gabebuckmaster/nixie_clock/firmware/Generic_F042Cx/variant.cpp

/*
 *******************************************************************************
 * Copyright (c) 2019, STMicroelectronics
 * All rights reserved.
 *
 * This software component is licensed by ST under BSD 3-Clause license,
 * the "License"; You may not use this file except in compliance with the
 * License. You may obtain a copy of the License at:
 *                        opensource.org/licenses/BSD-3-Clause
 *
 *******************************************************************************
 */

#include "pins_arduino.h"

#ifdef __cplusplus
extern "C" {
#endif

// Digital PinName array
// This array allows to wrap Arduino pin number(Dx or x)
// to STM32 PinName (PX_n)
// Arbitrarily chosen to be same as bluepill
const PinName digitalPin[] = {
  PB_9,  //D0
  PB_8,  //D1
  PB_7,  //D2
  PB_6,  //D3
  PB_5,  //D4
  PB_4,  //D5
  PB_3,  //D6
  PA_15, //D7
  PA_12, //D8 - USB DP
  PA_11, //D9 - USB DM
  PA_10, //D10
  PA_9,  //D11
  PA_8,  //D12
  PB_15, //D13
  PB_14, //D14
  PB_13, //D15
  PB_12, //D16
  /* Right side */
  PC_13, //D17
  PC_14, //D18
  PC_15, //D19
  PA_0,  //D20/A0
  PA_1,  //D21/A1
  PA_2,  //D22/A2
  PA_3,  //D23/A3
  PA_4,  //D24/A4
  PA_5,  //D25/A5
  PA_6,  //D26/A6
  PA_7,  //D27/A7
  PB_0,  //D28/A8
  PB_1,  //D29/A9
  PB_10, //D30
  PB_11, //D31
  PB_2,  //D32
  PA_13, //D33 - SWDI0
  PA_14, //D34 - SWCLK
};

// If analog pins are not contiguous in the digitalPin array:
// Add the analogInputPin array without defining NUM_ANALOG_FIRST
// Analog (Ax) pin number array
// where x is the index to retrieve the digital pin number
/*
const uint32_t analogInputPin[] = {
  //PXn, //Ax = Dx
  2, //A0 = Dx
  8, //A1 = Dy
  3  //A2 = Dz
}
 */

#ifdef __cplusplus
}
#endif

// ----------------------------------------------------------------------------

#ifdef __cplusplus
extern "C" {
#endif

/**
  * @brief  System Clock Configuration
  * @param  None
  * @retval None
  */
WEAK void SystemClock_Config(void)
{
  RCC_OscInitTypeDef RCC_OscInitStruct = {0};
  RCC_ClkInitTypeDef RCC_ClkInitStruct = {0};
  RCC_PeriphCLKInitTypeDef PeriphClkInit = {0};

  /** Initializes the CPU, AHB and APB busses clocks
  */
  RCC_OscInitStruct.OscillatorType = RCC_OSCILLATORTYPE_HSI|RCC_OSCILLATORTYPE_HSI14
                              |RCC_OSCILLATORTYPE_HSI48|RCC_OSCILLATORTYPE_LSI;
  RCC_OscInitStruct.HSIState = RCC_HSI_ON;
  RCC_OscInitStruct.HSI48State = RCC_HSI48_ON;
  RCC_OscInitStruct.HSI14State = RCC_HSI14_ON;
  RCC_OscInitStruct.HSICalibrationValue = RCC_HSICALIBRATION_DEFAULT;
  RCC_OscInitStruct.HSI14CalibrationValue = 16;
  RCC_OscInitStruct.LSIState = RCC_LSI_ON;
  RCC_OscInitStruct.PLL.PLLState = RCC_PLL_NONE;
  if (HAL_RCC_OscConfig(&RCC_OscInitStruct) != HAL_OK)
  {
    Error_Handler();
  }
  /** Initializes the CPU, AHB and APB busses clocks
  */
  RCC_ClkInitStruct.ClockType = RCC_CLOCKTYPE_HCLK|RCC_CLOCKTYPE_SYSCLK
                              |RCC_CLOCKTYPE_PCLK1;
  RCC_ClkInitStruct.SYSCLKSource = RCC_SYSCLKSOURCE_HSI48;
  RCC_ClkInitStruct.AHBCLKDivider = RCC_SYSCLK_DIV1;
  RCC_ClkInitStruct.APB1CLKDivider = RCC_HCLK_DIV1;

  if (HAL_RCC_ClockConfig(&RCC_ClkInitStruct, FLASH_LATENCY_1) != HAL_OK)
  {
    Error_Handler();
  }
  PeriphClkInit.PeriphClockSelection = RCC_PERIPHCLK_USB|RCC_PERIPHCLK_USART1
                              |RCC_PERIPHCLK_I2C1|RCC_PERIPHCLK_RTC;
  PeriphClkInit.Usart1ClockSelection = RCC_USART1CLKSOURCE_PCLK1;
  PeriphClkInit.I2c1ClockSelection = RCC_I2C1CLKSOURCE_HSI;
  PeriphClkInit.RTCClockSelection = RCC_RTCCLKSOURCE_LSI;
  PeriphClkInit.UsbClockSelection = RCC_USBCLKSOURCE_HSI48;

  if (HAL_RCCEx_PeriphCLKConfig(&PeriphClkInit) != HAL_OK)
  {
    Error_Handler();
  }
}

#ifdef __cplusplus
}
#endif
